Ecrypted-Data/Overload_Command/机械组资料/M3打印件预留尺寸.png

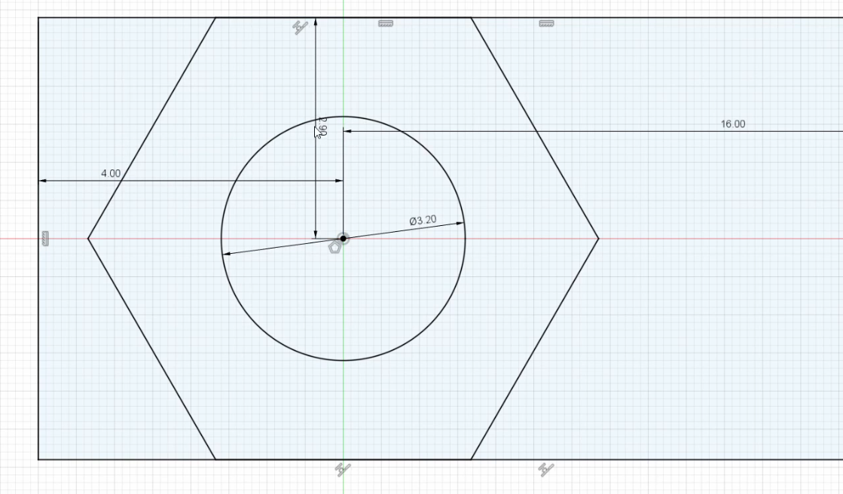
机械组资料/M3打印件预留尺寸.png
