Ecrypted-Data/Overload_Command/机械组资料/平头小螺丝参数.jpg

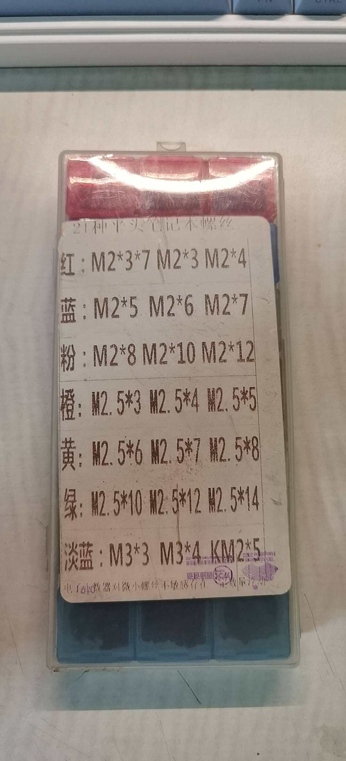
机械组资料/平头小螺丝参数.jpg
