Ecrypted-Data/Overload_Command/机械组资料/滚珠轴承参数.jpg

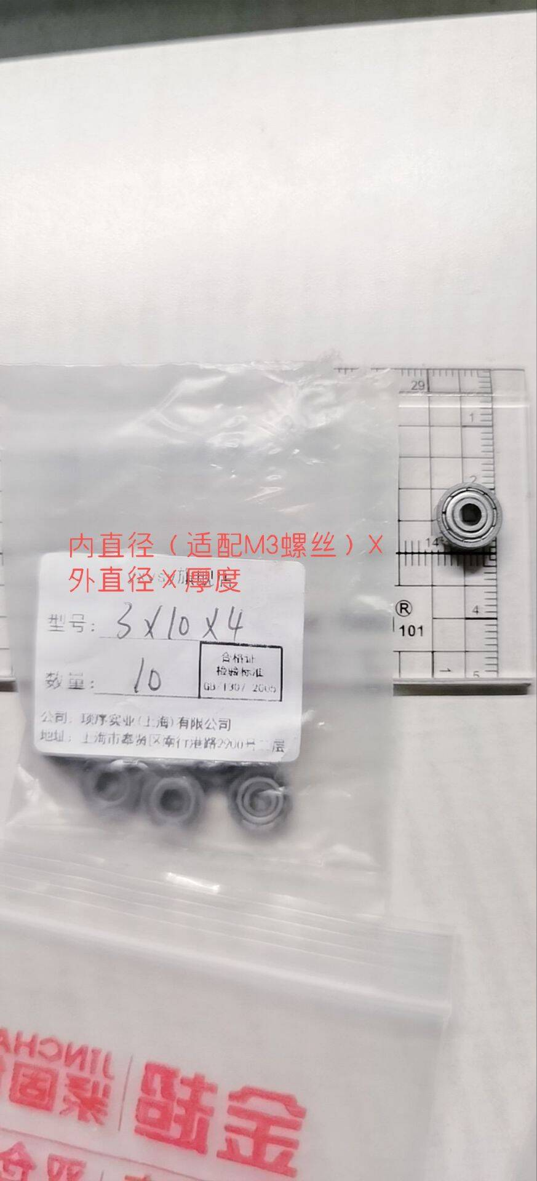
机械组资料/滚珠轴承参数.jpg
