Ecrypted-Data/Overload_Command/电控组资料/PS2 按键定义.png

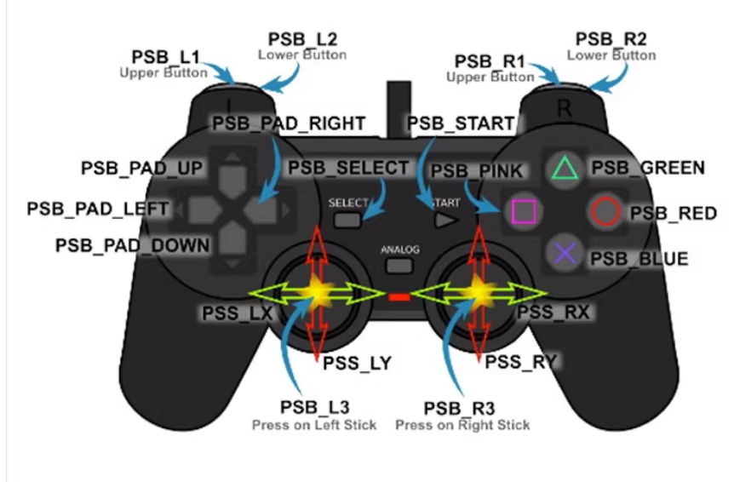
电控组资料/PS2 按键定义.png
