Ecrypted-Data/Overload_Command/硬件组资料/3节 电池盒尺寸.png

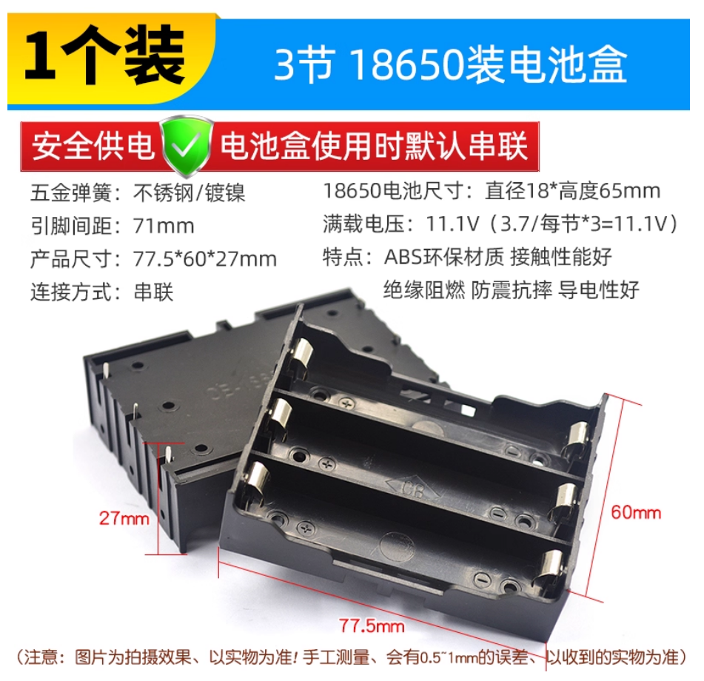
硬件组资料/3节 电池盒尺寸.png
