Ecrypted-Data/Overload_Command/硬件组资料/4节 电池盒尺寸.png

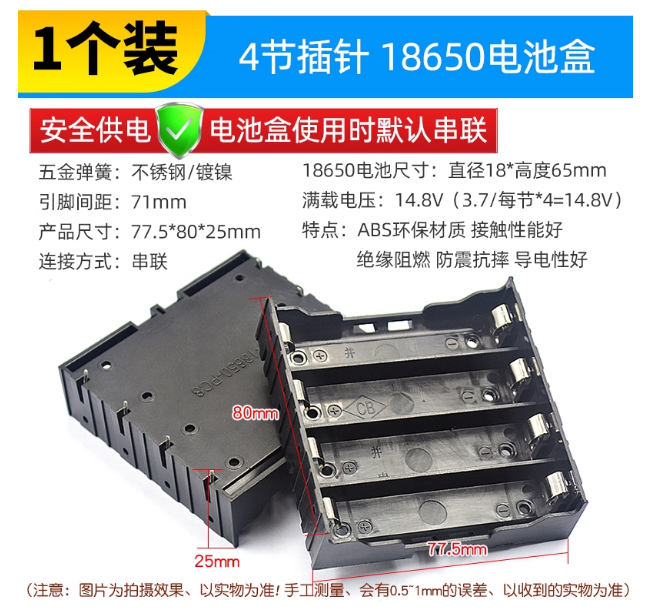
硬件组资料/4节 电池盒尺寸.png
