Ecrypted-Data/Overload_Command/硬件组资料/33GB-520电机 孔位孔径.png

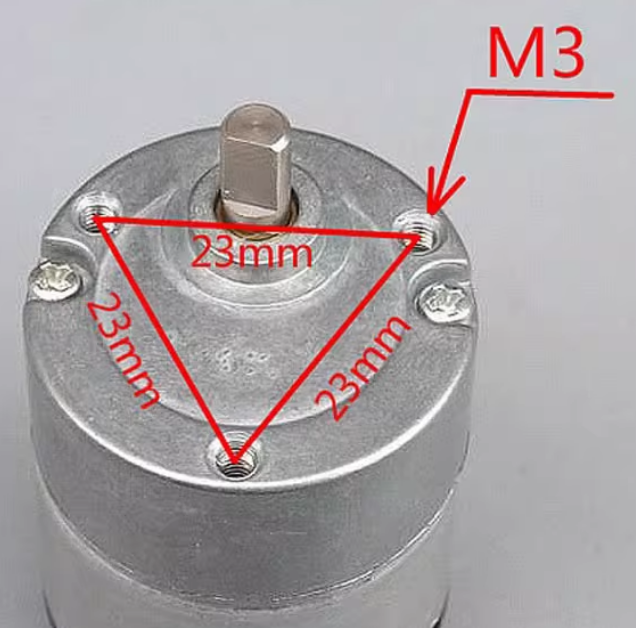
硬件组资料/33GB-520电机 孔位孔径.png
