Ecrypted-Data/Overload_Command/硬件组资料/33GB-520电机 设计图.png

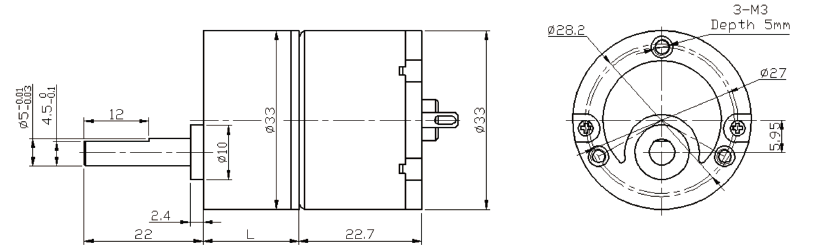
硬件组资料/33GB-520电机 设计图.png
