Ecrypted-Data/Overload_Command/硬件组资料/D4184 场效应管模块.png

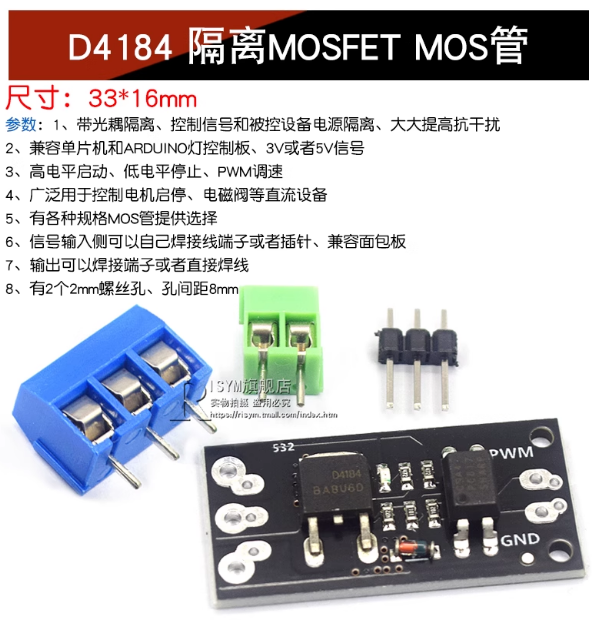
硬件组资料/D4184 场效应管模块.png
