Ecrypted-Data/Overload_Command/硬件组资料/DCE001 降压模块.png

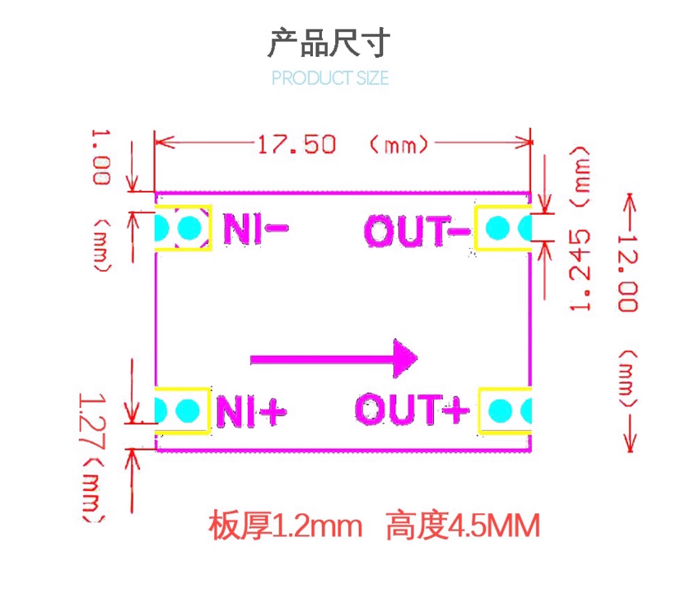
硬件组资料/DCE001 降压模块.png
