Ecrypted-Data/Overload_Command/硬件组资料/L298N 驱动板.png

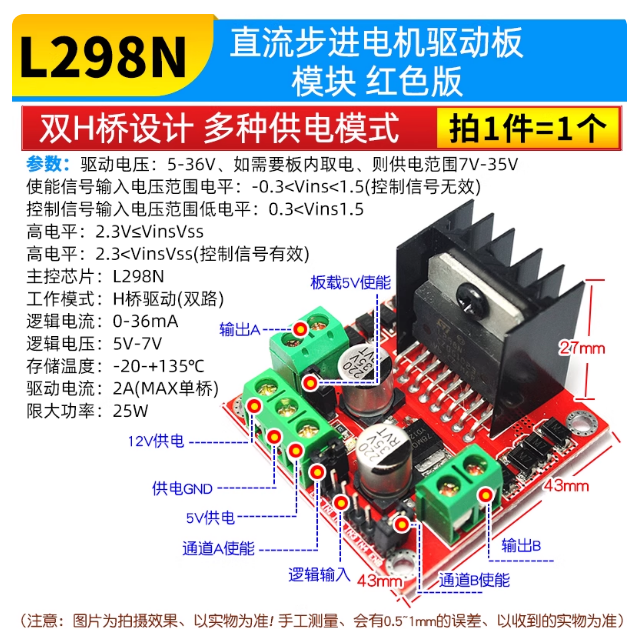
硬件组资料/L298N 驱动板.png
