Ecrypted-Data/Overload_Command/硬件组资料/N20 电机.png

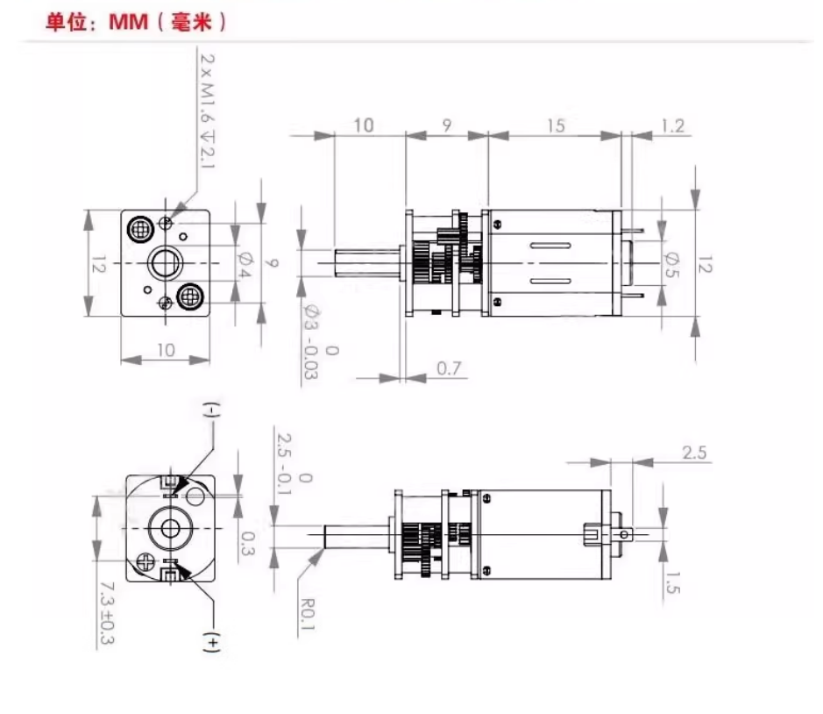
硬件组资料/N20 电机.png
