Ecrypted-Data/Overload_Command/硬件组资料/N20 紧固件尺寸.png

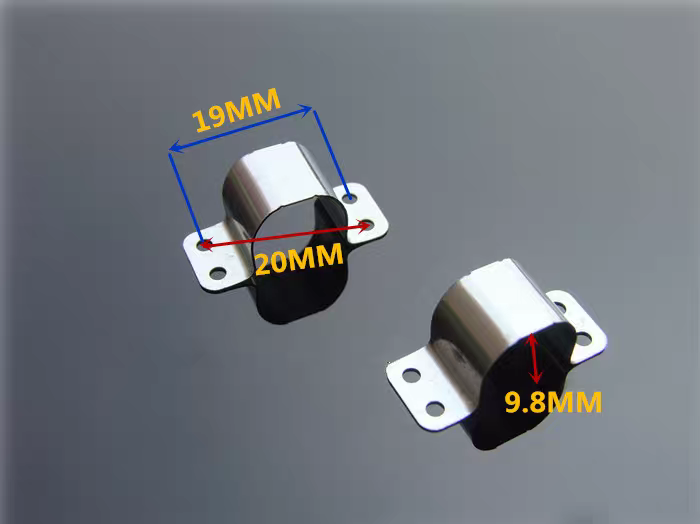
硬件组资料/N20 紧固件尺寸.png
