Ecrypted-Data/Overload_Command/硬件组资料/N20紧固件孔径.png

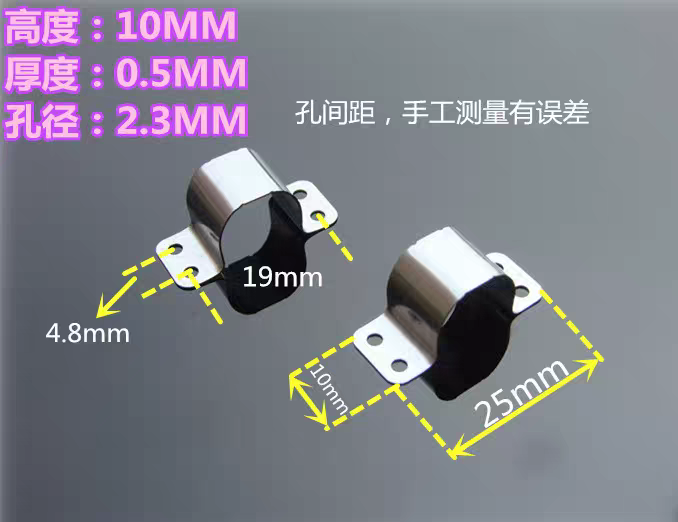
硬件组资料/N20紧固件孔径.png
