Ecrypted-Data/Overload_Command/硬件组资料/PS2 引脚定义.png

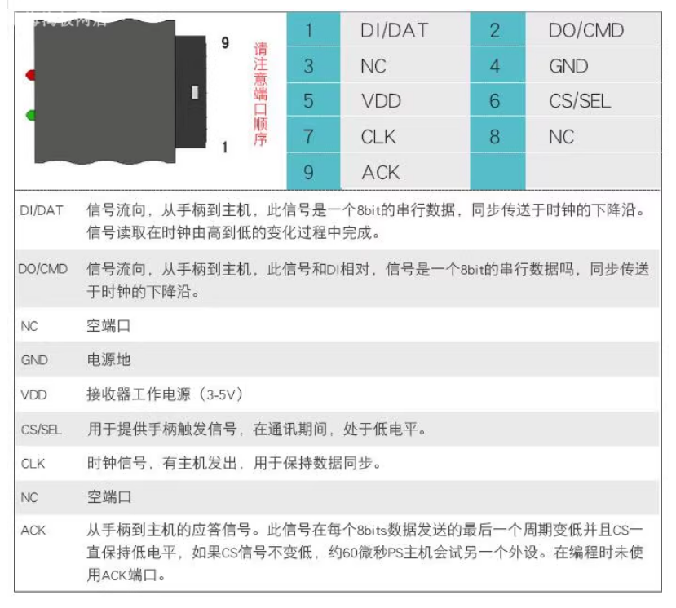
硬件组资料/PS2 引脚定义.png
