Ecrypted-Data/Overload_Command/硬件组资料/履带尺寸.png

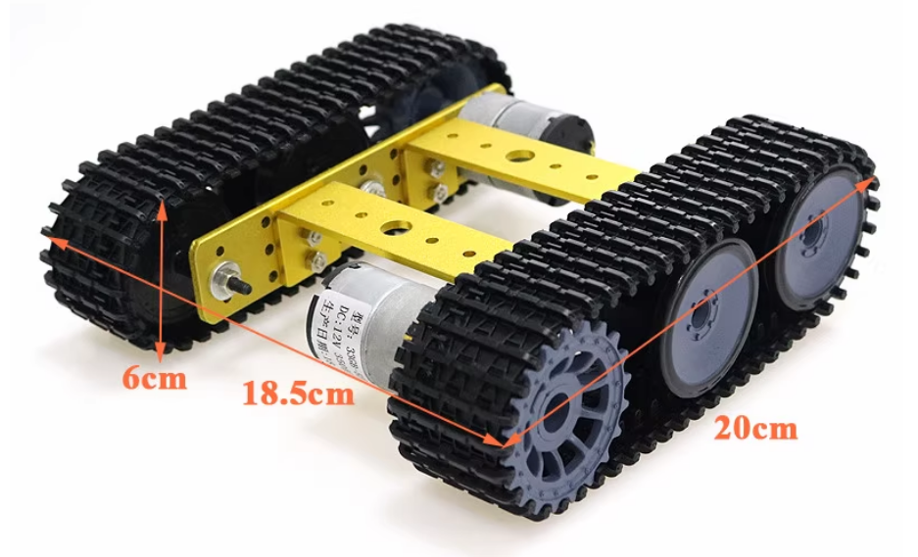
硬件组资料/履带尺寸.png
