Ecrypted-Data/Overload_Command/硬件组资料/无线控制直流单路继电器.png

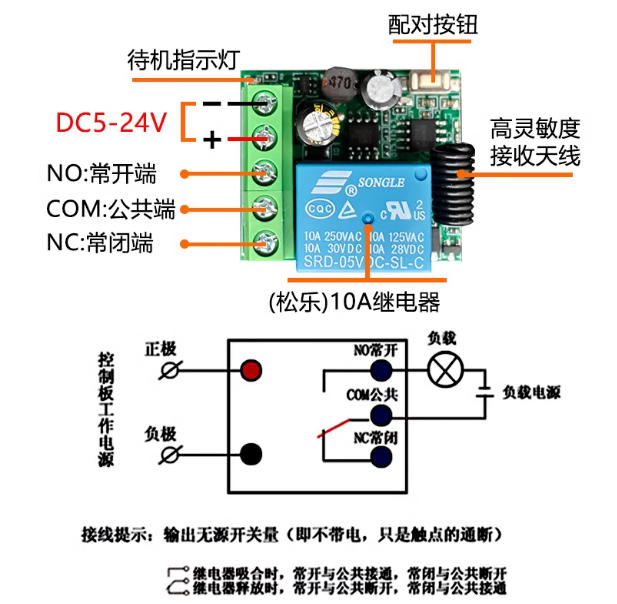
硬件组资料/无线控制直流单路继电器.png
