Ecrypted-Data/Overload_Command/硬件组资料/直柄碰撞传感器.png

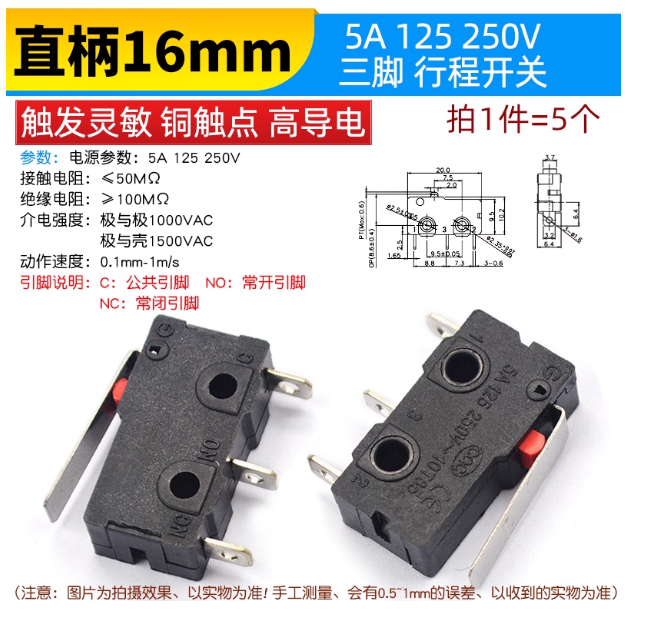
硬件组资料/直柄碰撞传感器.png
