Ecrypted-Data/Overload_Command/硬件组资料/碰撞传感器 KW8-3.png

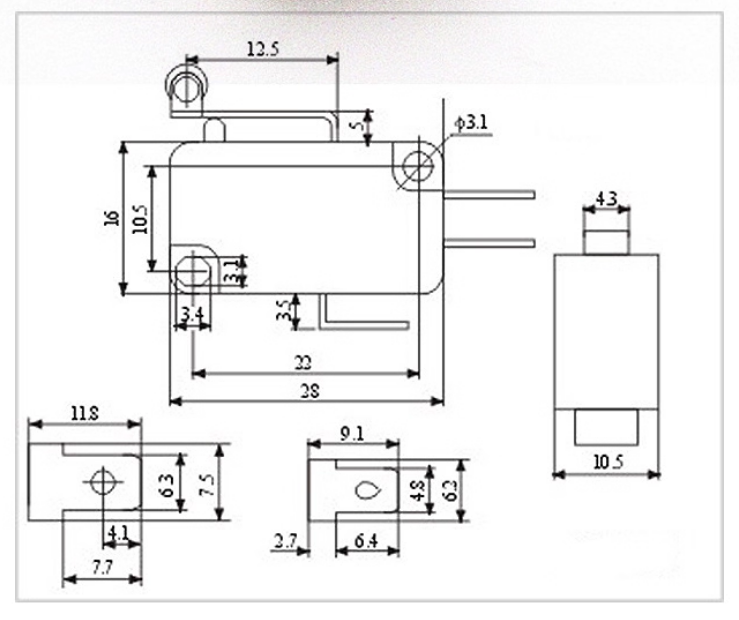
硬件组资料/碰撞传感器 KW8-3.png
