Ecrypted-Data/Overload_Command/硬件组资料/轮胎尺寸.png

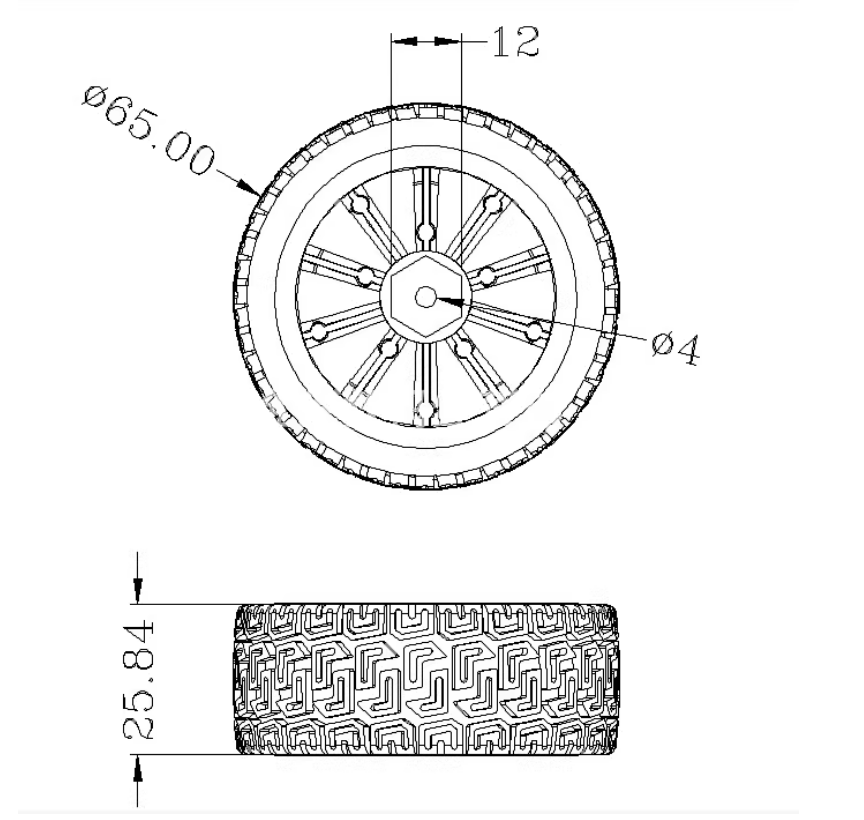
硬件组资料/轮胎尺寸.png
