Ecrypted-Data/Overload_Command/硬件组资料/轮胎马达总长.png

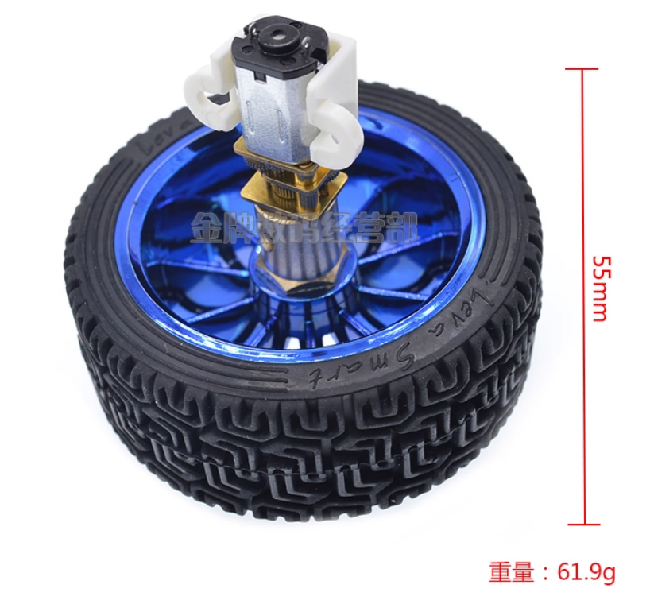
硬件组资料/轮胎马达总长.png
