Ecrypted-Data/Overload_Command/硬件组资料/黄铜六角联轴器.png

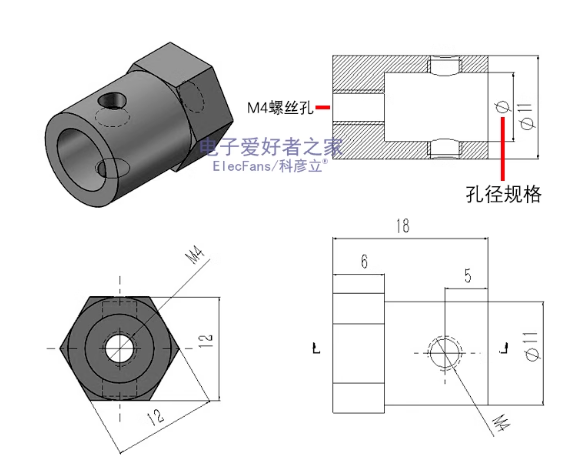
硬件组资料/黄铜六角联轴器.png
